alexkrejca/ec445_neuroguard/Aidan Moran/Documents/Screenshot 2025-11-02 192032.png

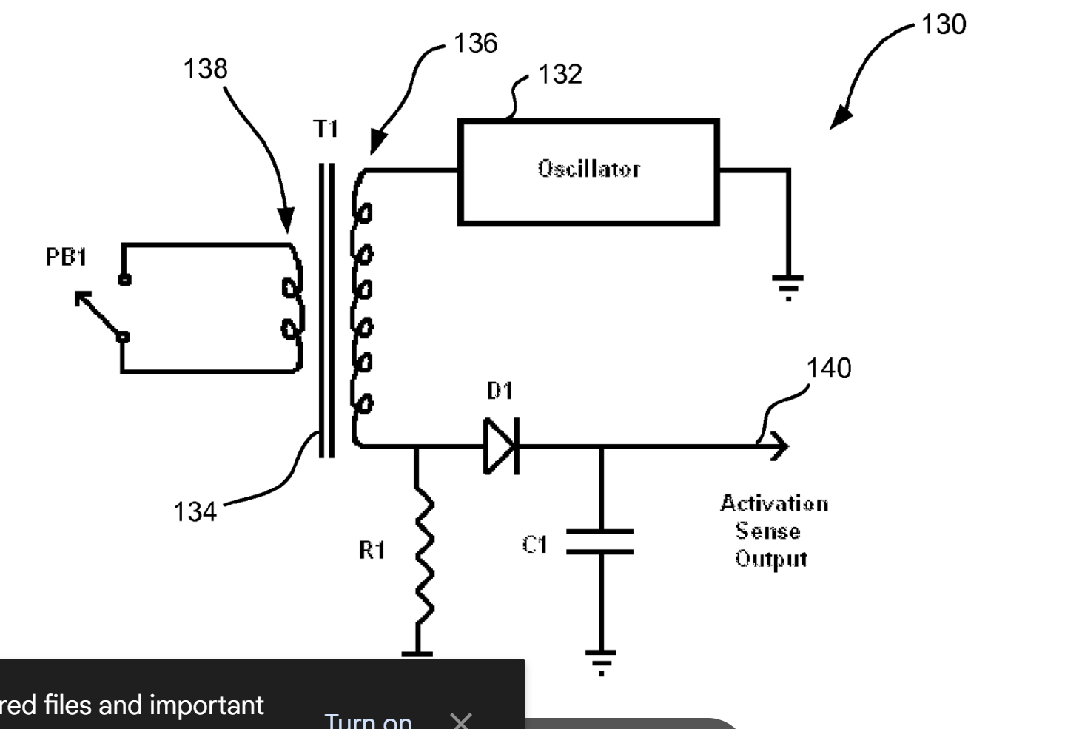
Aidan Moran/Documents/Screenshot 2025-11-02 192032.png
