alexkrejca/ec445_neuroguard/Aidan Moran/Documents/Screenshot 2025-11-03 134954.png

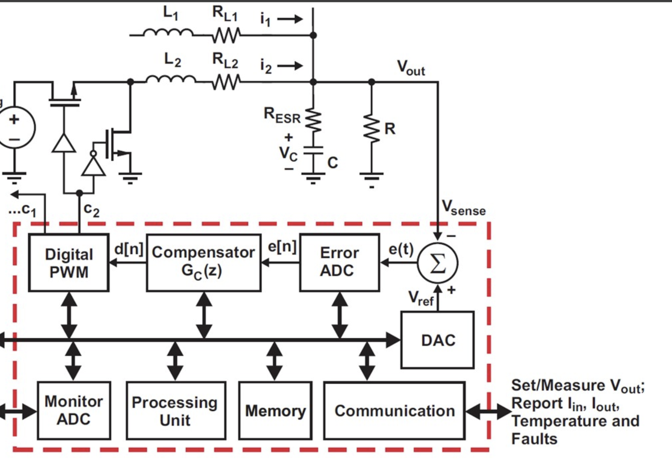
Aidan Moran/Documents/Screenshot 2025-11-03 134954.png
