alexkrejca/ec445_neuroguard/Aidan Moran/Documents/Screenshot 2025-11-05 091045.png

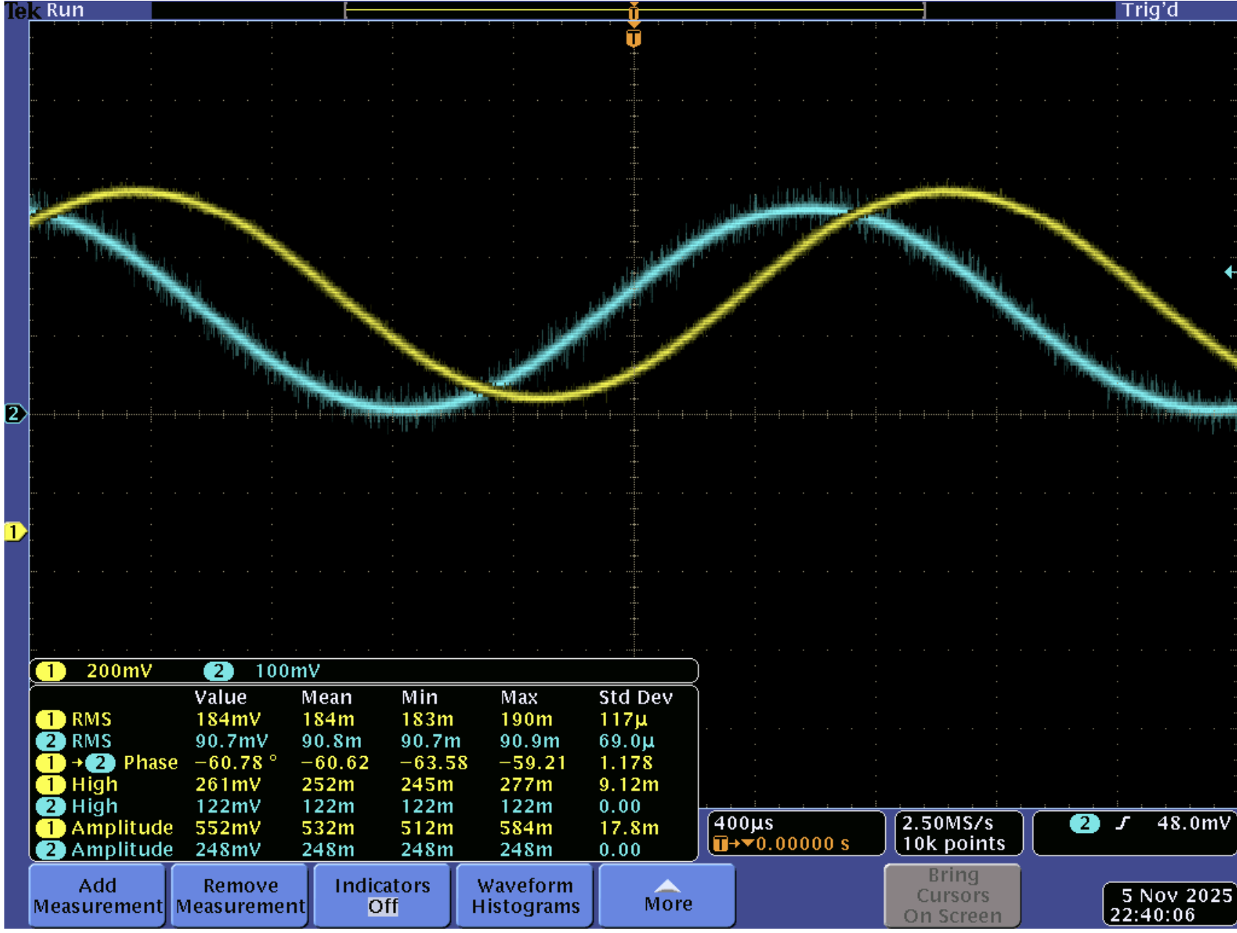
Aidan Moran/Documents/Screenshot 2025-11-05 091045.png
