alexkrejca/ec445_neuroguard/Aidan Moran/Documents/Screenshot 2025-11-05 092247.png

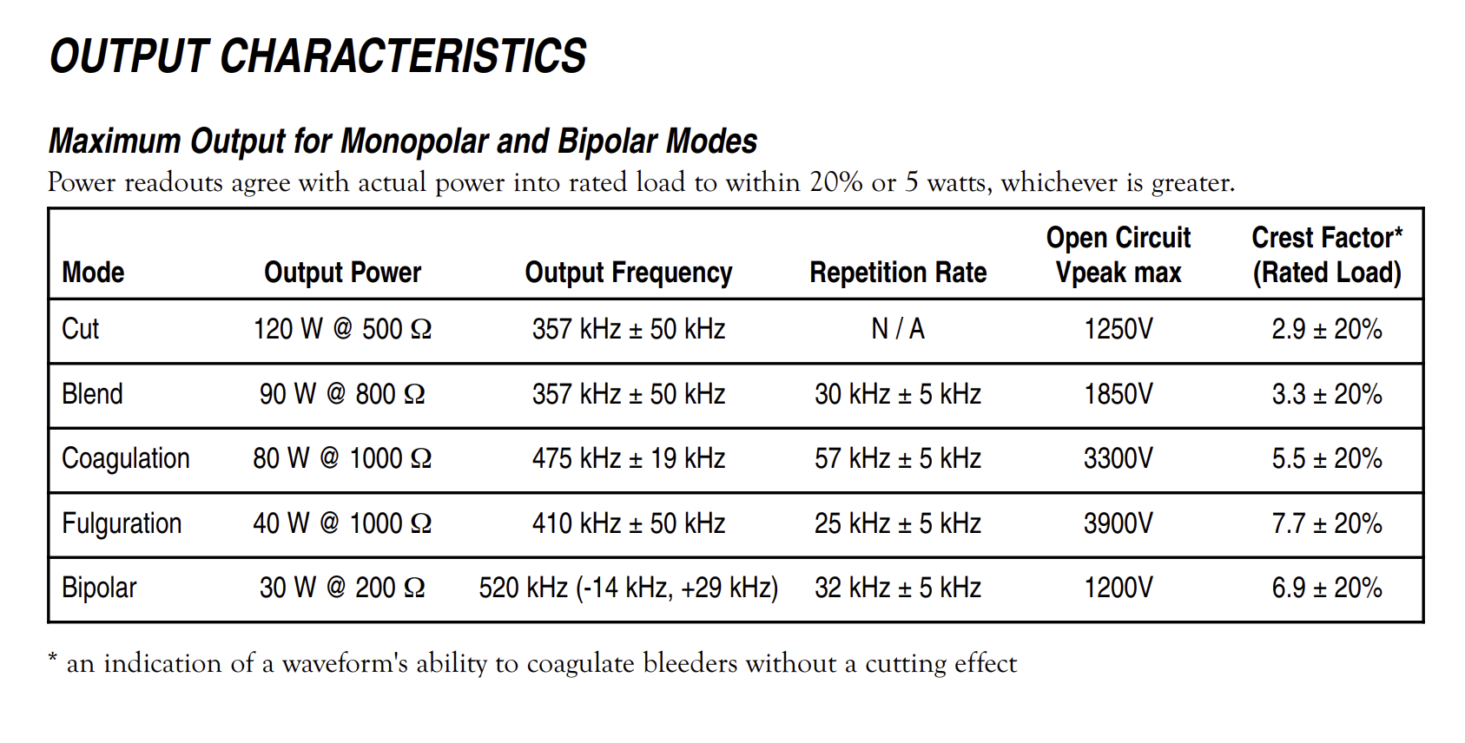
Aidan Moran/Documents/Screenshot 2025-11-05 092247.png
