alexkrejca/ec445_neuroguard/ECU_monitor_V2/BreadBoard_Occilisocpe.jpeg

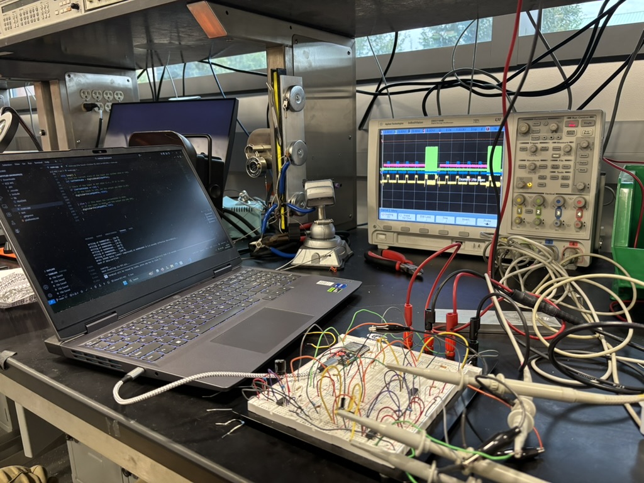
ECU_monitor_V2/BreadBoard_Occilisocpe.jpeg
