alexkrejca/ec445_neuroguard/ECU_monitor_V2/ECU_monitor_V2.asc

A1: inv; Vhigh=5 Vlow=0 Ref=2.5
BV_esu5: bv; V=V(carrier5) * V(modulator)
BV_esu: bv; V=V(carrier) * V(modulator)
C1: cap; 10p
C2: cap; 3.9n
C3: cap; 1n
C4: cap; 2.2n
C5: cap; 10n
C6: cap; 0.01µ
C7: cap; 100µF
C8: cap; 100µF
carrier5: voltage; SINE(2.5 2.5 357k)
carrier: voltage; SINE(925 925 357k)
D1: diode; 1N5817
D2: diode; 1N5817
D3: diode; 1N5817
M1: nmos; 2N7002
modulator: voltage; PULSE(0 1 1ms 1u 1u 1ms 5ms)
modulator_fast: voltage; PULSE(0 1 1ms 1u 1u 8u 40u)
R1: res; 10k
R2: res; 5.6k
R3: res; 3k
R4: res; 10k
R5: res; 10k
R6: res; 47k
R7: res; 15k
R8: res; 130k
R9: res; 2k
R10: res; 1k
R11: res; 5k
R12: res; 500k
R13: res; 1k
R14: res; 1k
R15: res; 43k
R16: res; 1k
R17: res; 100k
Rload: res; 10k
U1: LM393A
U2: NE555
U3: LTC1157
U4: LM393A
V1: voltage; 5
V2: voltage; 5
V3: voltage; 5
Named nets: 0, modulator, carrier, esu_out, divider_out, envelope, comp_out, carrier5, esu5_out, modulator_fast, pulse_0.1V, Output
.tran 20ms
